bwshockley/Mini-SAM/M4/MINI_SAM_D51_012.brd

## EAGLE design M4/MINI_SAM_D51_012.brd (2018-10-02)

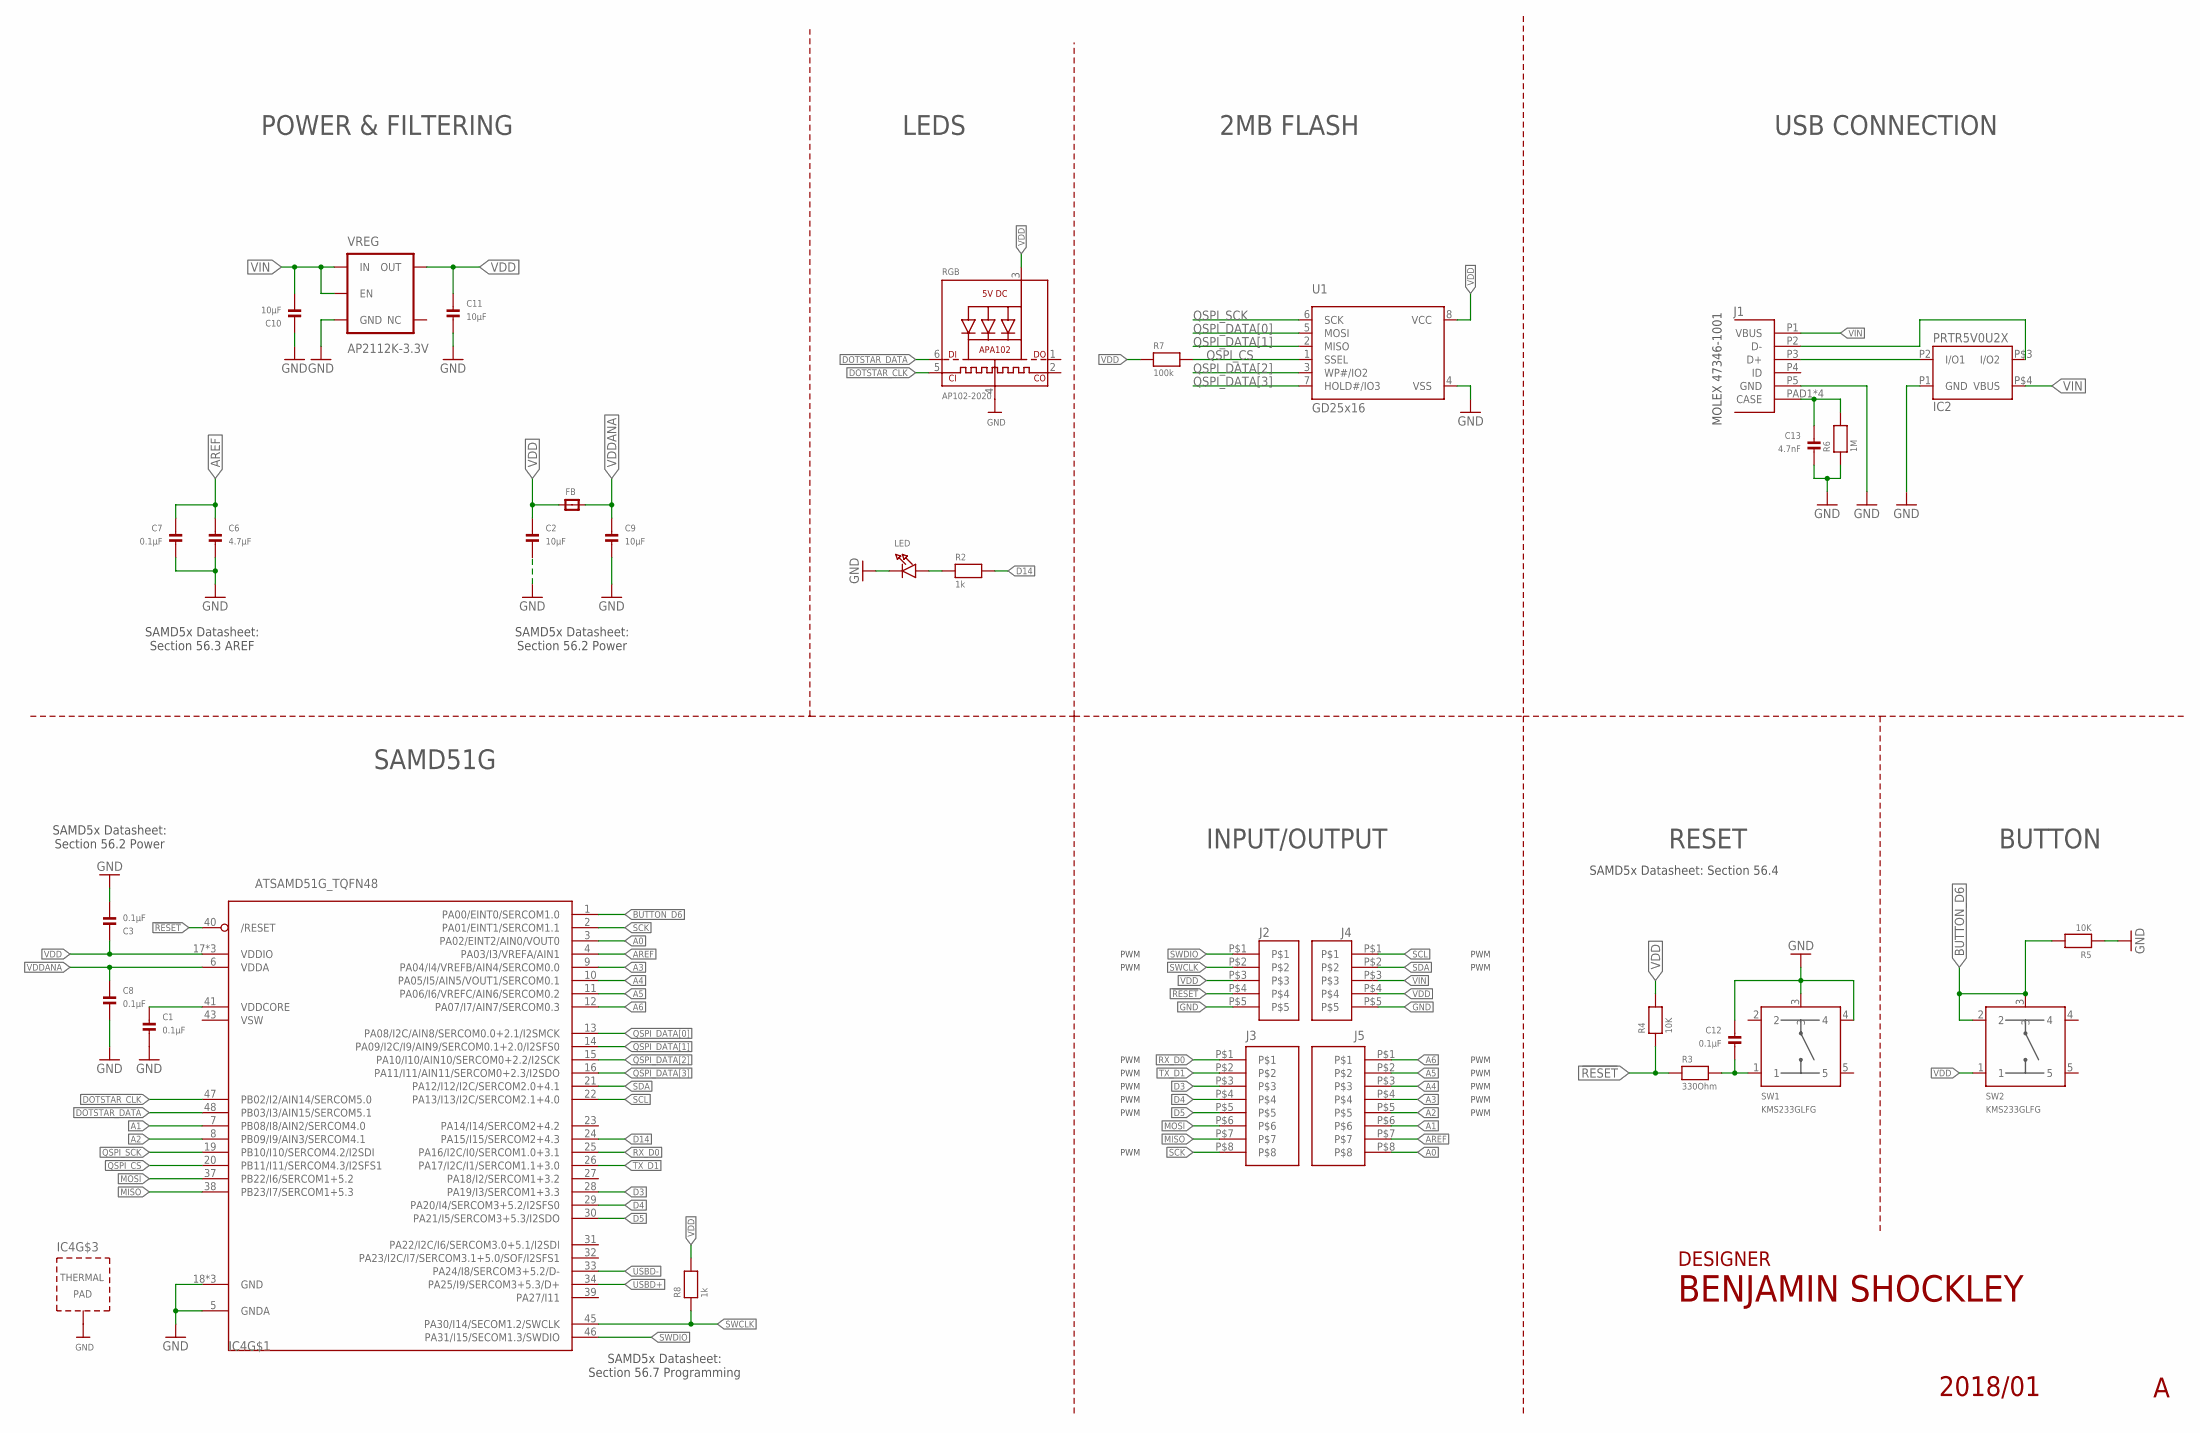
[picture p14: schematic MINI_SAM_D51_012.sch]

Parts:
C1, C3, C7, C8, C12: 0.1µF; _0603MP
C2, C9, C10, C11: 10µF; _0603MP
C6: 4.7µF; _0603MP
C13: 4.7nF; _0603MP
FB: FERRITE_0603MP; _0603MP
IC2: PRTR5V0U2X; SOT143B_REFLOW
IC4: ATSAMD51G_TQFN48; TQFN48_7MM
J1: MOLEX_47346-100147346; MOLEX_47346-1001
J2, J4: 1X5_HEADER_1.27MM
J3, J5: 1X8_HEADER_1.27MM
LED: LED0805_NOOUTLINE; CHIPLED_0805_NOOUTLINE
R2, R8: 1k; _0603MP
R3: 330Ohm; _0603MP
R4, R5: 10K; _0603MP
R6: 1M; _0603MP
R7: 100k; _0603MP
RGB: AP102-2020; APA102_2020
SW1, SW2: KMS233GLFG; KMS_SWITCH
U1: GD25x16; USON8
VREG: AP2112K-3.3V; SOT23-5

Connections:
!RESET: IC4.40 (/RESET), J2.P$4, R3.1, R4.1
A0: IC4.3 (PA02/EINT2/AIN0/VOUT0), J5.P$8
A1: IC4.7 (PB08/I8/AIN2/SERCOM4.0), J5.P$6
A2: IC4.8 (PB09/I9/AIN3/SERCOM4.1), J5.P$5
A3: IC4.9 (PA04/I4/VREFB/AIN4/SERCOM0.0), J5.P$4
A4: IC4.10 (PA05/I5/AIN5/VOUT1/SERCOM0.1), J5.P$3
A5: IC4.11 (PA06/I6/VREFC/AIN6/SERCOM0.2), J5.P$2
A6: IC4.12 (PA07/I7/AIN7/SERCOM0.3), J5.P$1
AREF: C6.1, C7.1, IC4.4 (PA03/I3/VREFA/AIN1), J5.P$7
BUTTON_D6: IC4.1 (PA00/EINT0/SERCOM1.0), R5.2, SW2.2, SW2.3
D3: IC4.28 (PA19/I3/SERCOM1+3.3), J3.P$3
D4: IC4.29 (PA20/I4/SERCOM3+5.2/I2SFS0), J3.P$4
D5: IC4.30 (PA21/I5/SERCOM3+5.3/I2SDO), J3.P$5
D14: IC4.24 (PA15/I15/SERCOM2+4.3), R2.2
DOTSTAR_CLK: IC4.47 (PB02/I2/AIN14/SERCOM5.0), RGB.5 (CKI)
DOTSTAR_DATA: IC4.48 (PB03/I3/AIN15/SERCOM5.1), RGB.6 (DI)
GND: C1.2, C2.2, C3.2, C6.2, C7.2, C8.2, C9.2, C10.1, C11.2, C12.1, C13.2, IC2.P1 (GND), IC4.5 (GNDA), IC4.18 (GND), IC4.35 (GND), IC4.42 (GND), IC4.THERMAL (TP), J1.P5 (GND), J2.P$5, J4.P$5, LED.C, R5.1, R6.1, RGB.4 (GND), SW1.3, SW1.4, U1.4 (VSS), VREG.2 (GND)
MISO: IC4.38 (PB23/I7/SERCOM1+5.3), J3.P$7
MOSI: IC4.37 (PB22/I6/SERCOM1+5.2), J3.P$6
unnamed: C13.1, J1.PAD1 (CASE), J1.PAD2 (CASE), J1.PAD3 (CASE), J1.PAD4 (CASE), R6.2
unnamed: LED.A, R2.1
unnamed: C12.2, R3.2, SW1.1
unnamed: C1.1, IC4.41 (VDDCORE)
QSPI_CS: IC4.20 (PB11/I11/SERCOM4.3/I2SFS1), R7.2, U1.1 (SSEL)
QSPI_DATA[0]: IC4.13 (PA08/I2C/AIN8/SERCOM0.0+2.1/I2SMCK), U1.5 (MOSI)
QSPI_DATA[1]: IC4.14 (PA09/I2C/I9/AIN9/SERCOM0.1+2.0/I2SFS0), U1.2 (MISO)
QSPI_DATA[2]: IC4.15 (PA10/I10/AIN10/SERCOM0+2.2/I2SCK), U1.3 (WP#/IO2)
QSPI_DATA[3]: IC4.16 (PA11/I11/AIN11/SERCOM0+2.3/I2SDO), U1.7 (HOLD#/IO3)
QSPI_SCK: IC4.19 (PB10/I10/SERCOM4.2/I2SDI), U1.6 (SCK)
RX_D0: IC4.25 (PA16/I2C/I0/SERCOM1.0+3.1), J3.P$1
SCK: IC4.2 (PA01/EINT1/SERCOM1.1), J3.P$8
SCL: IC4.22 (PA13/I13/I2C/SERCOM2.1+4.0), J4.P$1
SDA: IC4.21 (PA12/I12/I2C/SERCOM2.0+4.1), J4.P$2
SWCLK: IC4.45 (PA30/I14/SECOM1.2/SWCLK), J2.P$2, R8.1
SWDIO: IC4.46 (PA31/I15/SECOM1.3/SWDIO), J2.P$1
TX_D1: IC4.26 (PA17/I2C/I1/SERCOM1.1+3.0), J3.P$2
USBD+: IC2.P2 (I/O1), IC4.34 (PA25/I9/SERCOM3+5.3/D+), J1.P3 (D+)
USBD-: IC2.P$3 (I/O2), IC4.33 (PA24/I8/SERCOM3+5.2/D-), J1.P2 (D-)
VDD: C2.1, C3.1, C11.1, FB.1, IC4.17 (VDDIO), IC4.36 (VDDIO), IC4.44 (VDDIO), J2.P$3, J4.P$4, R4.2, R7.1, R8.2, RGB.3 (VDD), SW2.1, U1.8 (VCC), VREG.5 (OUT)
VDDANA: C8.1, C9.1, FB.2, IC4.6 (VDDA)
VIN: C10.2, IC2.P$4 (VBUS), J1.P1 (VBUS), J4.P$3, VREG.1 (IN), VREG.3 (EN)
VSW: IC4.43 (VSW)

Notes on the sheet:
INPUT/OUTPUT
RESET
POWER & FILTERING
SAMD51G
LEDS
USB CONNECTION
MOLEX 47346-1001
BUTTON
DESIGNER
SAMD5x Datasheet: Section 56.4
2MB FLASH
SAMD5x Datasheet: Section 56.3 AREF
SAMD5x Datasheet: Section 56.2 Power
SAMD5x Datasheet: Section 56.7 Programming
PWM

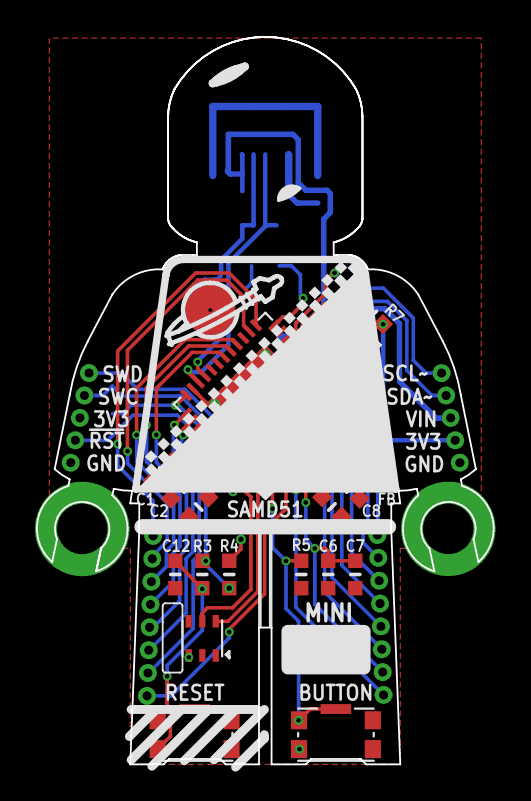
[picture p15: board MINI_SAM_D51_012.brd from above]

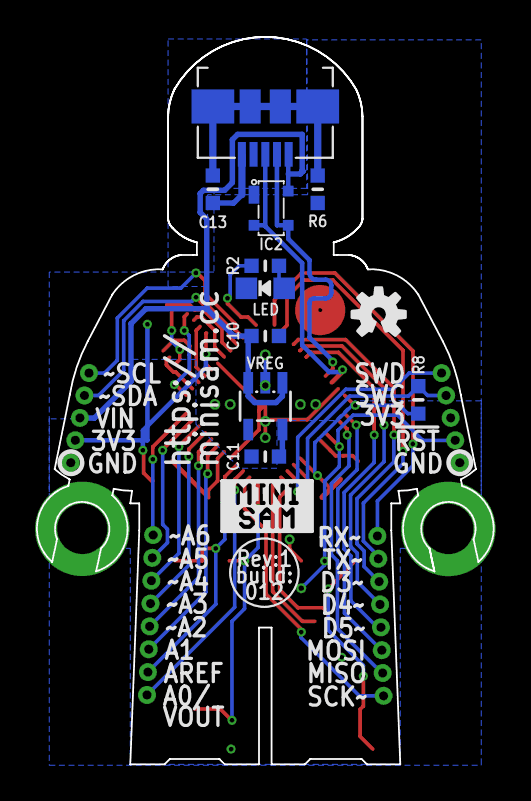
[picture p16: board MINI_SAM_D51_012.brd from below]

Board: 2 copper layers, 25.4 x 40.4 mm, 33 parts (11 on the bottom side), 41 nets.

Other parts of the board:
U$3: OSHW-LOGO-S
