bwshockley/Mini-SAM/M4/MINI_SAM_D51_001.brd

## EAGLE design M4/MINI_SAM_D51_001.brd (2018-07-25)

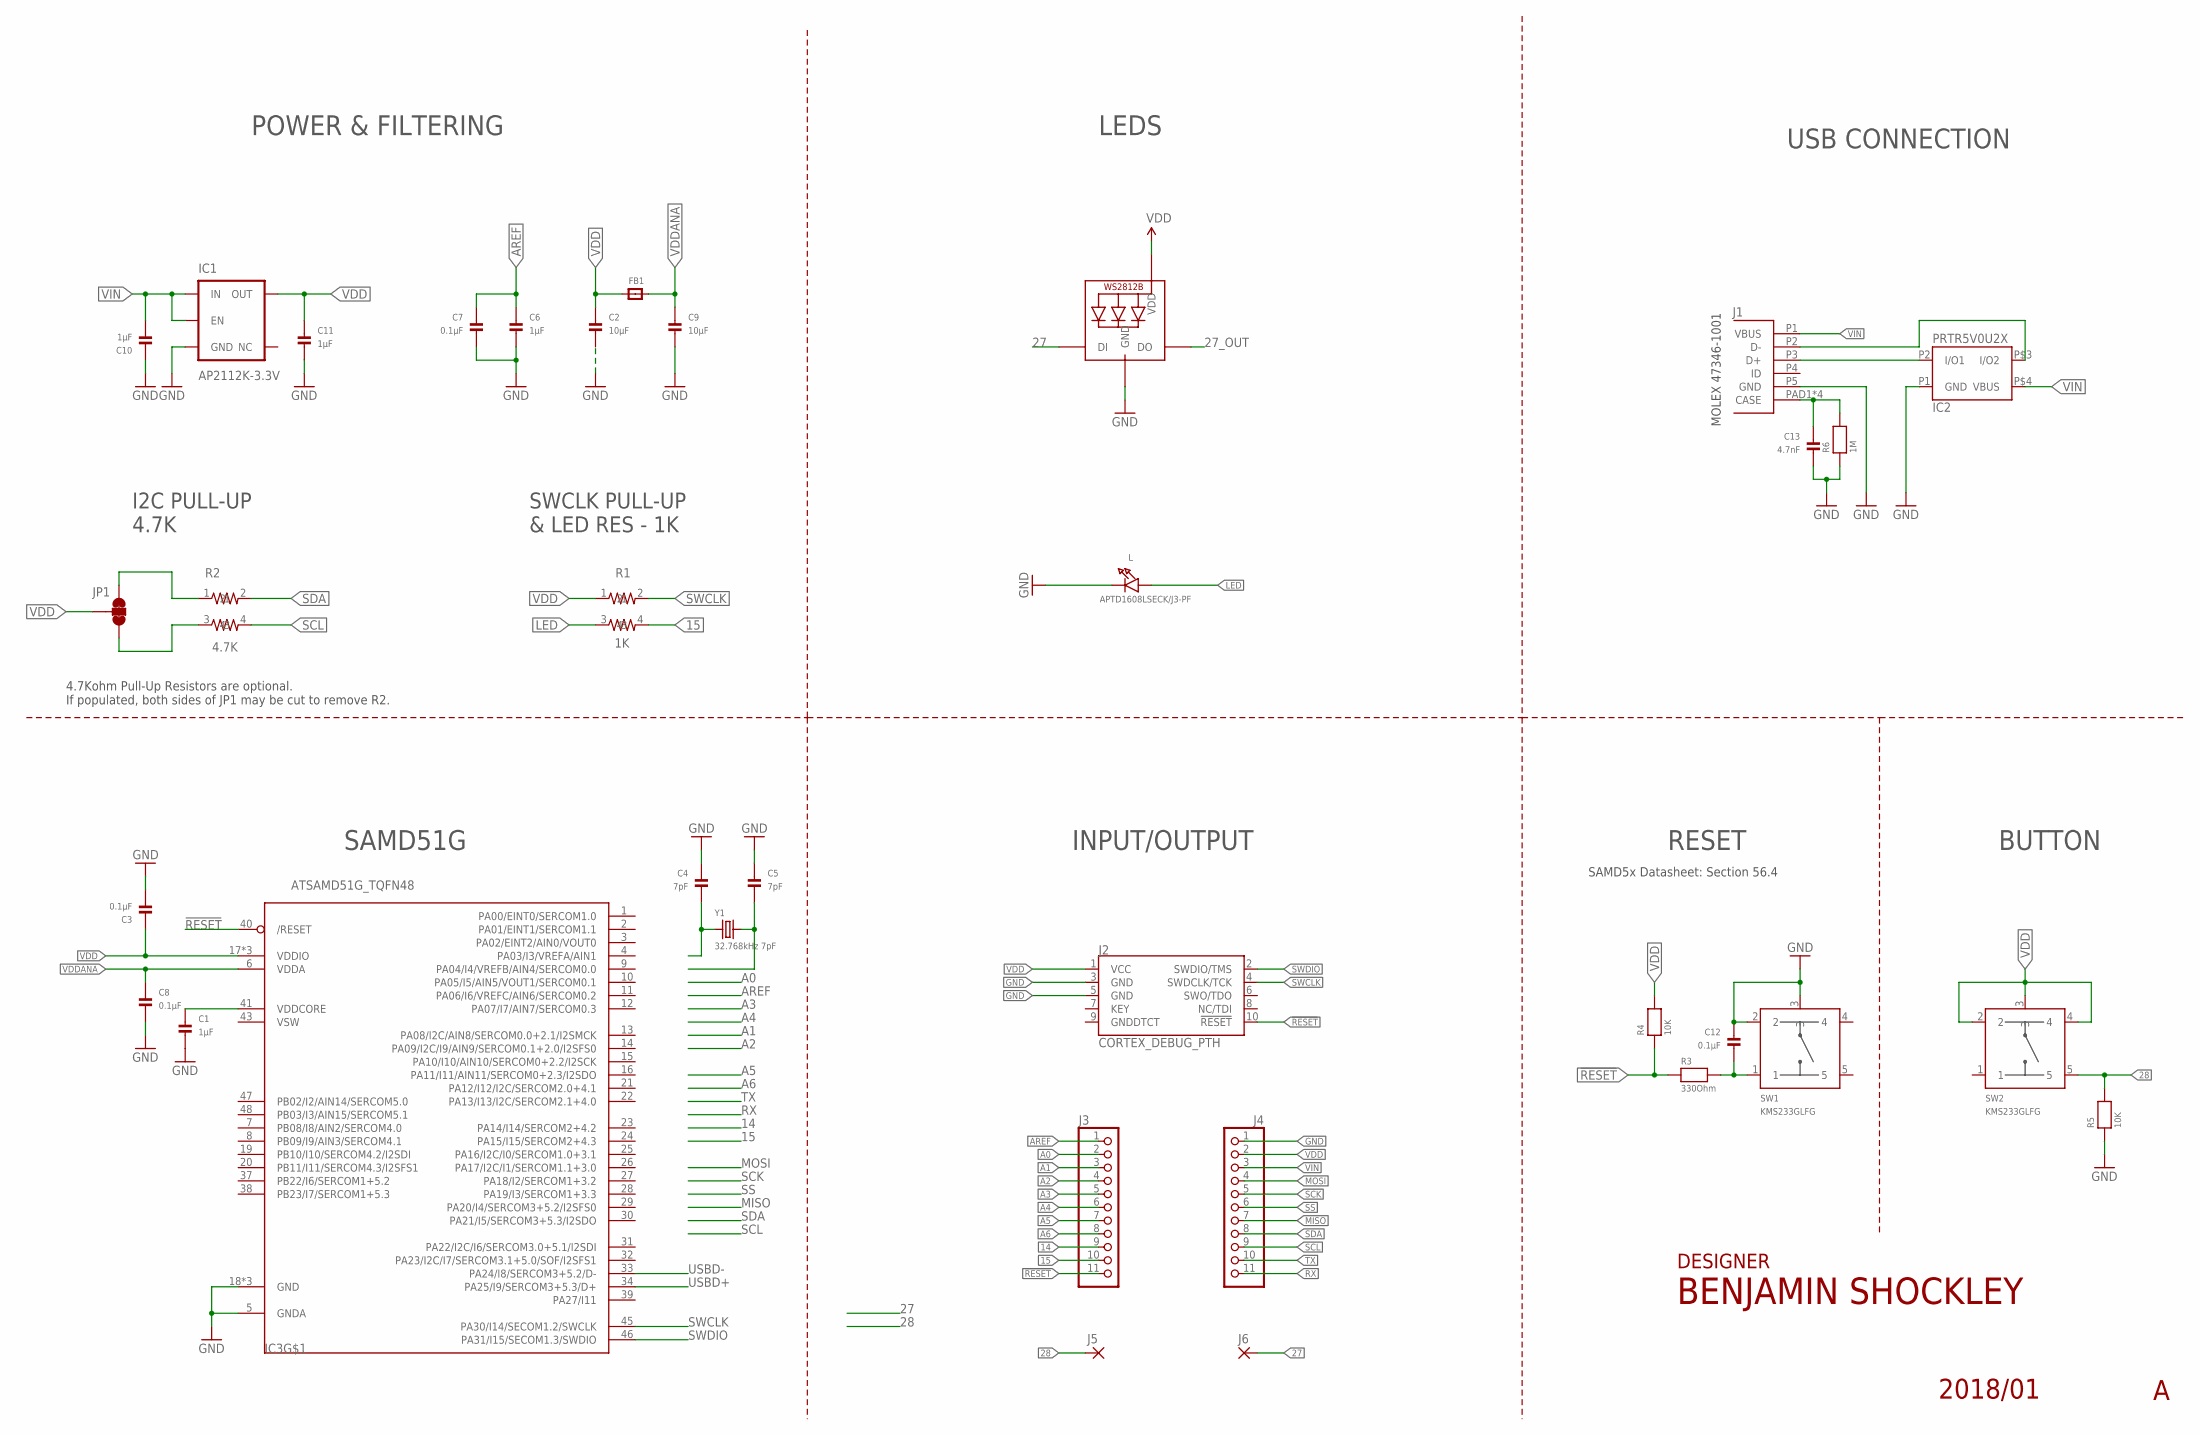
[picture p17: schematic MINI_SAM_D51_001.sch]

Parts:
C1, C6, C10, C11: 1µF; _0805MP
C2, C9: 10µF; _0805MP
C3, C7, C8, C12: 0.1µF; _0805MP
C4, C5: 7pF; _0805MP
C13: 4.7nF; _0805MP
FB1: FERRITE_0805MP; _0805MP
IC1: AP2112K-3.3V; SOT23-5
IC2: PRTR5V0U2X; SOT143B_REFLOW
IC3: ATSAMD51G_TQFN48; TQFN48_7MM
J1: MOLEX_47346-100147346; MOLEX_47346-1001
J2: CORTEX_DEBUG_PTH; 2X5-PTH-1.27MM
J3, J4: PINHD-1X111X11_SMT; 1X11_SMT
J5, J6: FR11_PAD2MMX1MM; SMD2MMX1MM
JP1: JUMPER-SMT_3_2-NC_TRACE_NO-SILK; SMT-JUMPER_3_2-NC_TRACE_NO-SILK
L: APTD1608LSECK/J3-PF; CHIPLED_0603_NOOUTLINE
R1: 1K; RESISTOR_ARRAY_0606
R2: 4.7K; RESISTOR_ARRAY_0606
R3: 330Ohm; _0805MP
R4, R5: 10K; _0805MP
R6: 1M; _0805MP
RGB: WS2812B3535; LED3535
SW1, SW2: KMS233GLFG; KMS_SWITCH
Y1: 32.768kHz 7pF; _0805MP

Connections:
14: J3.9
15: J3.10, R1.4
27: J6.P$1, RGB.1 (DI)
27_OUT: RGB.3 (DO)
28: J5.P$1, R5.2, SW2.5
!RESET: IC3.40 (/RESET), J2.10 (!RESET), J3.11, R3.1, R4.1
A0: J3.2
A1: J3.3
A2: J3.4
A3: J3.5
A4: J3.6
A5: J3.7
A6: J3.8
AREF: C6.1, C7.1, J3.1
GND: C1.2, C2.2, C3.2, C4.1, C5.1, C6.2, C7.2, C8.2, C9.2, C10.1, C11.2, C12.1, C13.2, IC1.2 (GND), IC2.P1 (GND), IC3.5 (GNDA), IC3.18 (GND), IC3.35 (GND), IC3.42 (GND), J1.P5 (GND), J2.3 (GND), J2.5 (GND), J4.1, L.C, R5.1, R6.1, RGB.4 (GND), SW1.2, SW1.3; also elsewhere on the board
LED: L.A, R1.3
MISO: J4.7
MOSI: J4.4
unnamed: C4.2, Y1.1
unnamed: C13.1, J1.PAD1 (CASE), J1.PAD2 (CASE), J1.PAD3 (CASE), J1.PAD4 (CASE), R6.2
unnamed: JP1.1, R2.1
unnamed: C12.2, R3.2, SW1.1
unnamed: C5.2, Y1.2
unnamed: JP1.3, R2.3
unnamed: C1.1, IC3.41 (VDDCORE)
RX: J4.11
SCK: J4.5
SCL: J4.9, R2.4
SDA: J4.8, R2.2
SS: J4.6
SWCLK: IC3.45 (PA30/I14/SECOM1.2/SWCLK), J2.4 (SWDCLK/TCK), R1.2
SWDIO: IC3.46 (PA31/I15/SECOM1.3/SWDIO), J2.2 (SWDIO/TMS)
TP: IC3.THERMAL (TP)
TX: J4.10
USBD+: IC2.P2 (I/O1), IC3.34 (PA25/I9/SERCOM3+5.3/D+), J1.P3 (D+)
USBD-: IC2.P$3 (I/O2), IC3.33 (PA24/I8/SERCOM3+5.2/D-), J1.P2 (D-)
VDD: C2.1, C3.1, C11.1, FB1.1, IC1.5 (OUT), IC3.17 (VDDIO), IC3.36 (VDDIO), IC3.44 (VDDIO), J2.1 (VCC), J4.2, JP1.2, R1.1, R4.2, RGB.2 (VDD), SW2.2, SW2.3, SW2.4
VDDANA: C8.1, C9.1, FB1.2, IC3.6 (VDDA)
VIN: C10.2, IC1.1 (IN), IC1.3 (EN), IC2.P$4 (VBUS), J1.P1 (VBUS), J4.3
VSW: IC3.43 (VSW); also elsewhere on the board

Notes on the sheet:
INPUT/OUTPUT
RESET
POWER & FILTERING
SAMD51G
LEDS
USB CONNECTION
I2C PULL-UP 4.7K
MOLEX 47346-1001
BUTTON
SWCLK PULL-UP & LED RES - 1K
DESIGNER
4.7Kohm Pull-Up Resistors are optional. If populated, both sides of JP1 may be cut to remove R2.
SAMD5x Datasheet: Section 56.4

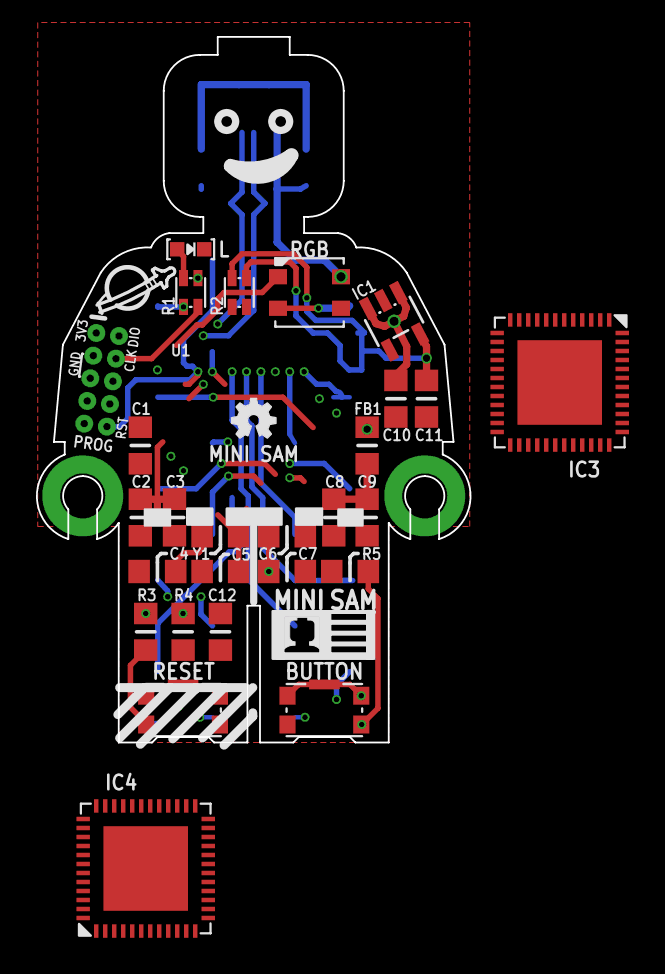
[picture p18: board MINI_SAM_D51_001.brd from above]

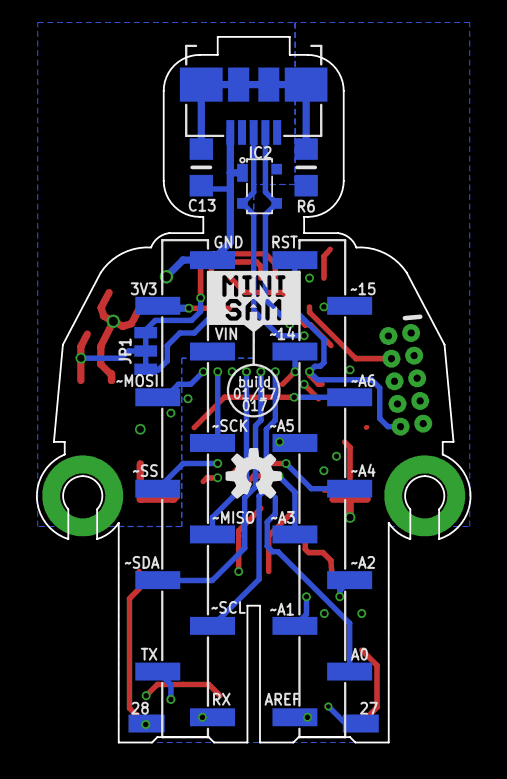
[picture p19: board MINI_SAM_D51_001.brd from below]

Board: 4 copper layers, 24.1 x 39.2 mm, 38 parts (10 on the bottom side), 25 nets.

Other parts of the board:
IC4: ATSAMD51G_TQFN48; TQFN48_7MM
U$1: OSHW-LOGO-MINI
U$3: OSHW-LOGO-S

Their connections:
GND: IC4.18, IC4.35, IC4.42, IC4.THERMAL; also elsewhere on the board
VDDIO: IC4.17, IC4.36, IC4.44
VSW: IC4.43; also elsewhere on the board
